elentok/iris-case/STLs/mid-layer-left.stl

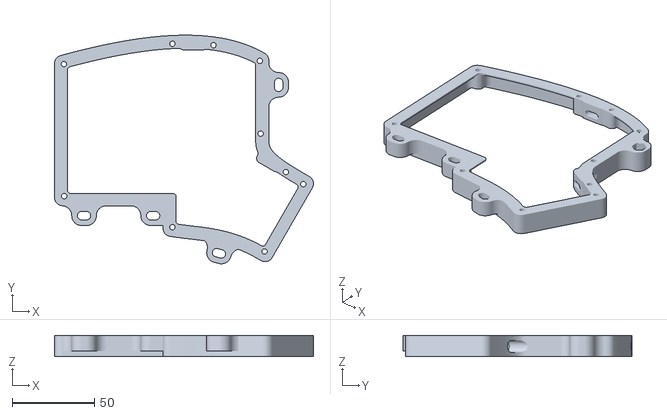
[picture p17: CAD file, 2024-01-20]
STLs/mid-layer-left.stl
157.4 x 139.0 x 12.8
