elentok/iris-case/STLs/foot-extender-17mm.stl

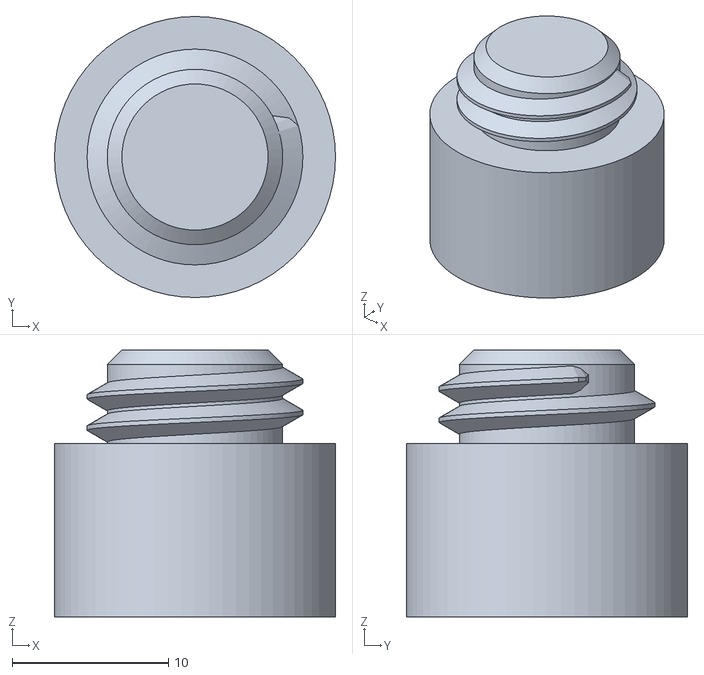
[picture p18: CAD file, 2024-01-20]
STLs/foot-extender-17mm.stl
18.0 x 18.0 x 17.1
